TimBergling07/Smart-Space-Occupancy-Sign/Smart Space Occupancy Sign/ESP32 Audio AI/SmartDoorPlate_SoundDetector/src/model.h

#pragma once
#include <cstdarg>
#include <stdint.h>
namespace Eloquent {
    namespace ML {
        namespace Port {
            class RandomForest {
                public:
                    /**
                    * Predict class for features vector
                    */
                    int predict(float *x) {
                        uint8_t votes[2] = { 0 };
                        // tree #1
                        if (x[1] <= 1.0) {
                            if (x[0] <= 0.00296847359277308) {
                                if (x[3] <= 0.36685626208782196) {
                                    votes[1] += 1;
                                }

                                else {
                                    votes[0] += 1;
                                }
                            }

                            else {
                                if (x[3] <= 0.4065352827310562) {
                                    votes[1] += 1;
                                }

                                else {
                                    if (x[3] <= 0.5555106699466705) {
                                        if (x[3] <= 0.4479355812072754) {
                                            votes[0] += 1;
                                        }

                                        else {
                                            votes[0] += 1;
                                        }
                                    }

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

                        return classIdx;
                    }

                    /**
                    * Predict readable class name
                    */
                    const char* predictLabel(float *x) {
                        return idxToLabel(predict(x));
                    }

                    /**
                    * Convert class idx to readable name
                    */
                    const char* idxToLabel(uint8_t classIdx) {
                        switch (classIdx) {
                            case 0:
                            return "Empty";
                            case 1:
                            return "Occupied";
                            default:
                            return "Houston we have a problem";
                        }
                    }

                protected:
                };
            }
        }
    }
